amywork777/hardware-craft-night/designs/exports/kicad_src/flower/flower.kicad_sch

## KiCad design designs/exports/kicad_src/flower/flower.kicad_sch (2026-03-16)

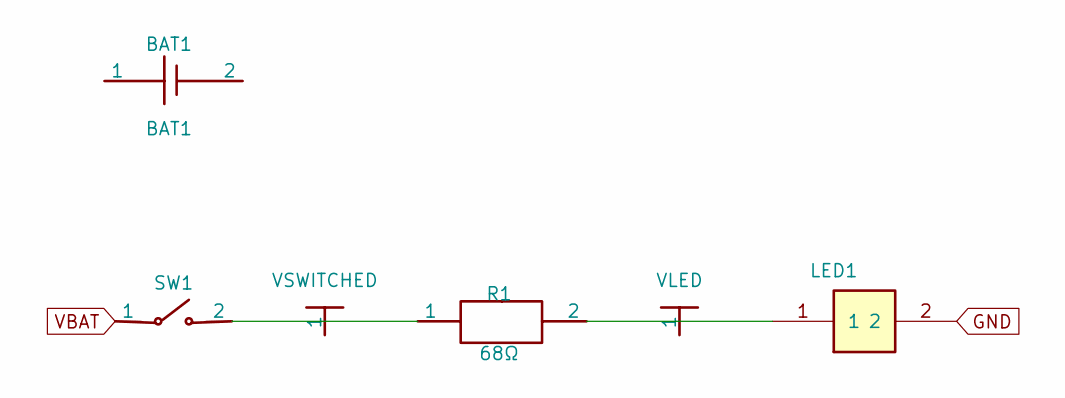
[picture p3: schematic flower.kicad_sch]

Parts:
BAT1: BAT1
LED1: LED1
R1: 68Ω
SW1: (no value)
VLED: VLED
VSWITCHED: VSWITCHED

Connections:
GND: LED1.2
unnamed: LED1.1, R1.2
unnamed: R1.1, SW1.2
VBAT: SW1.1
