amywork777/hardware-craft-night/designs/exports/kicad_src/heart/heart.kicad_sch

## KiCad design designs/exports/kicad_src/heart/heart.kicad_sch (2026-03-16)

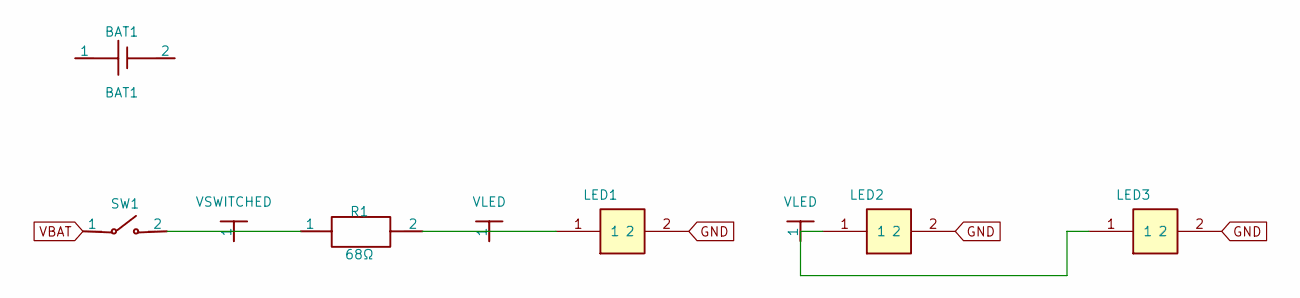
[picture p4: schematic heart.kicad_sch]

Parts:
BAT1: BAT1
LED1: LED1
LED2: LED2
LED3: LED3
R1: 68Ω
SW1: (no value)
VLED: VLED
VSWITCHED: VSWITCHED

Connections:
GND: LED1.2, LED2.2, LED3.2
unnamed: LED1.1, R1.2
unnamed: LED2.1, LED3.1
unnamed: R1.1, SW1.2
VBAT: SW1.1
